sundberg84/AllHearingEar/hardware/3d model/Pyramid 0.2/20161116_210447.jpg

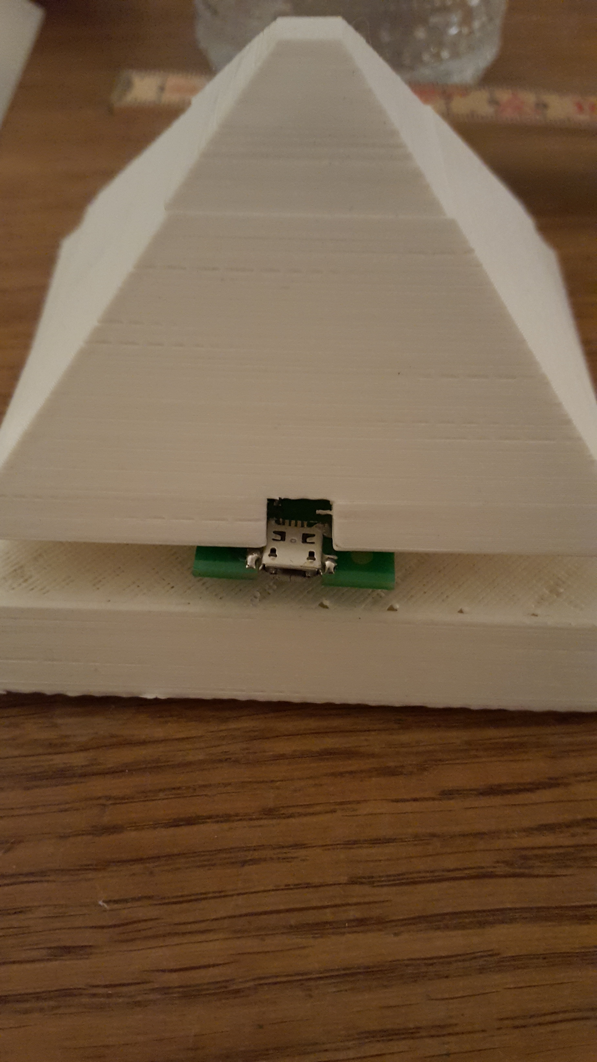
hardware/3d model/Pyramid 0.2/20161116_210447.jpg
