sundberg84/AllHearingEar/hardware/PCB/UsbSticka/Res/Max9814ada.JPG

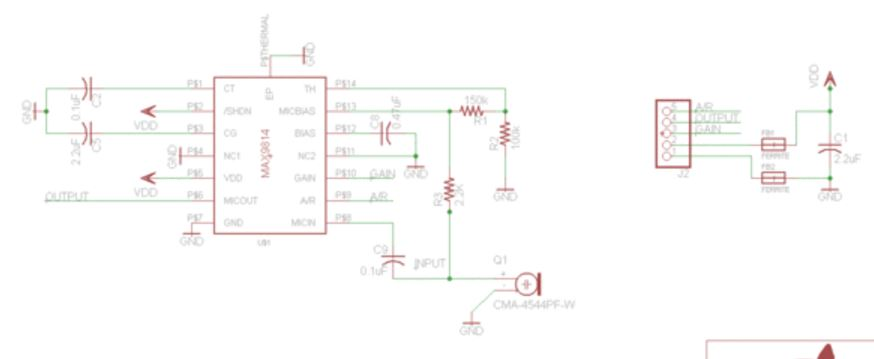
hardware/PCB/UsbSticka/Res/Max9814ada.JPG
