sundberg84/AllHearingEar/Pictures/3dPyraLong.JPG

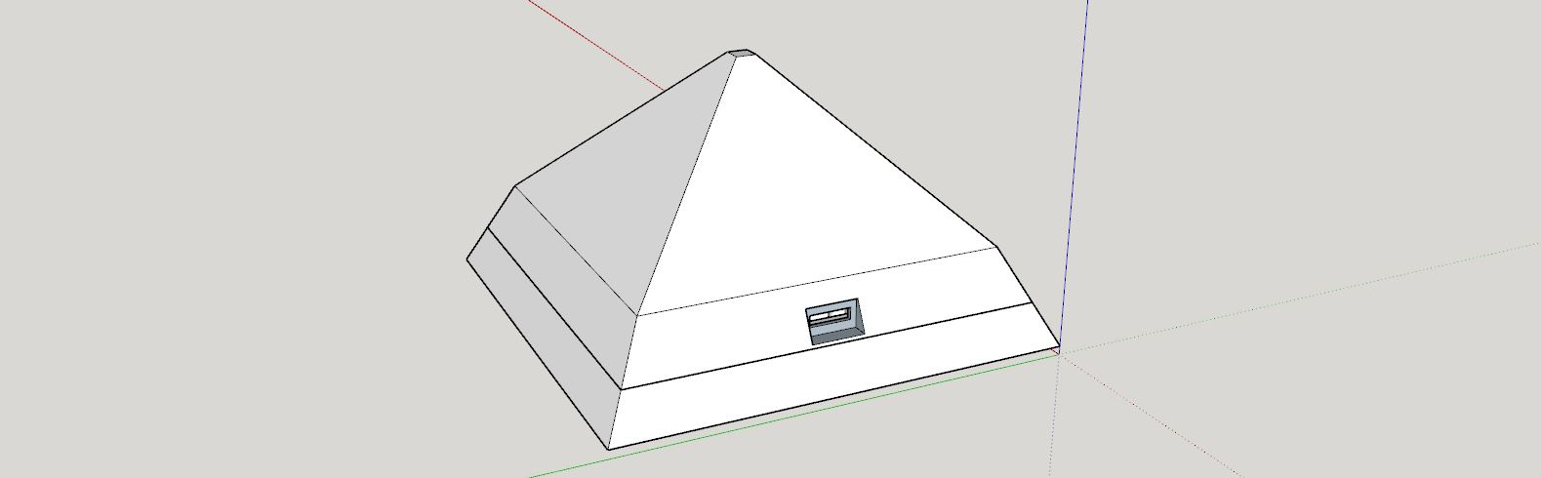
Pictures/3dPyraLong.JPG
