sundberg84/AllHearingEar/Pictures/3dPyraSquare.JPG

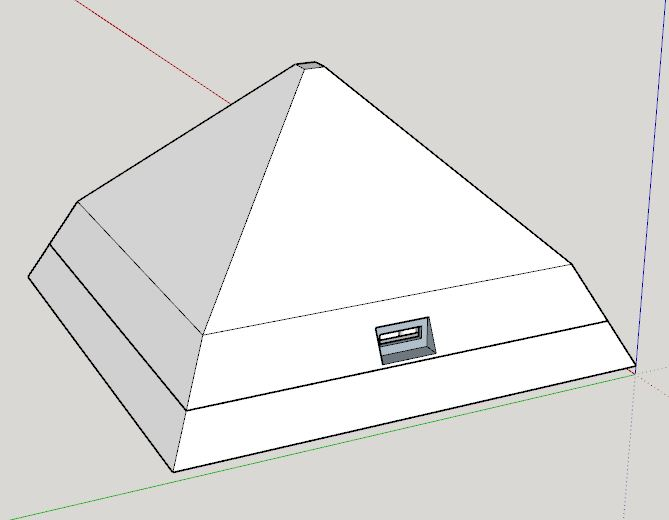
Pictures/3dPyraSquare.JPG
