sundberg84/AllHearingEar/Pictures/20160913_220625.jpg

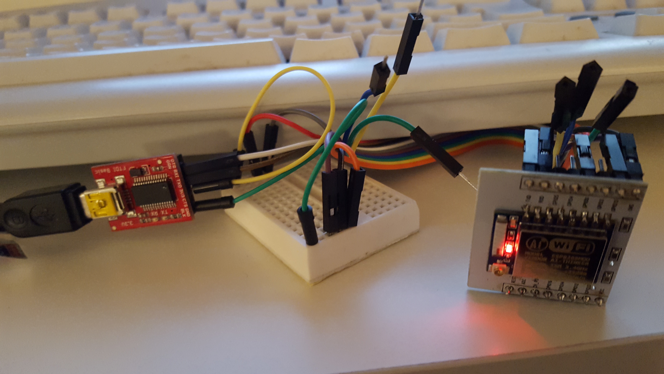
Pictures/20160913_220625.jpg
