sundberg84/AllHearingEar/Pictures/20160926_PCBtest.JPG

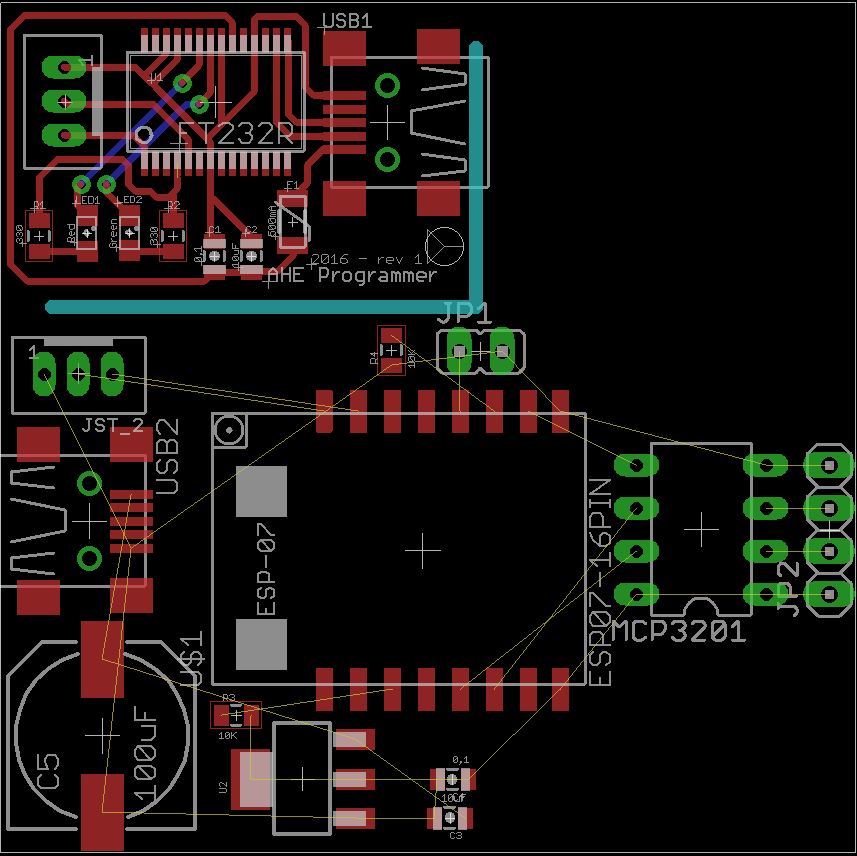
Pictures/20160926_PCBtest.JPG
