sundberg84/AllHearingEar/Pictures/20161007_163945.jpg

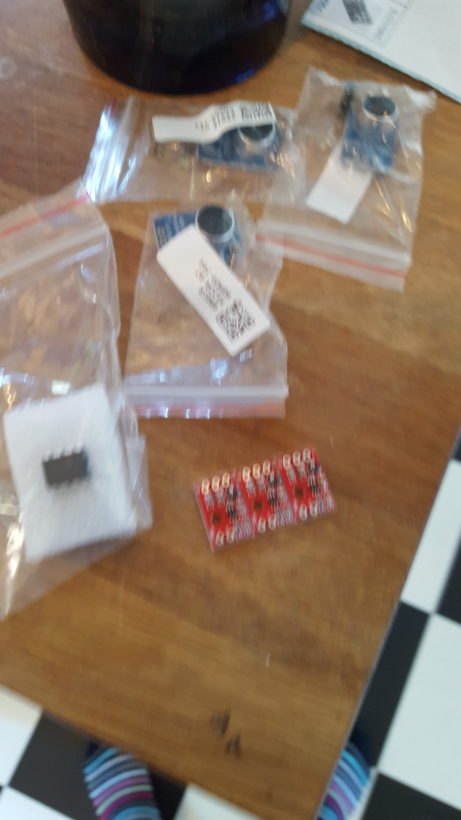
Pictures/20161007_163945.jpg
