sundberg84/AllHearingEar/Pictures/20161007_164515.jpg

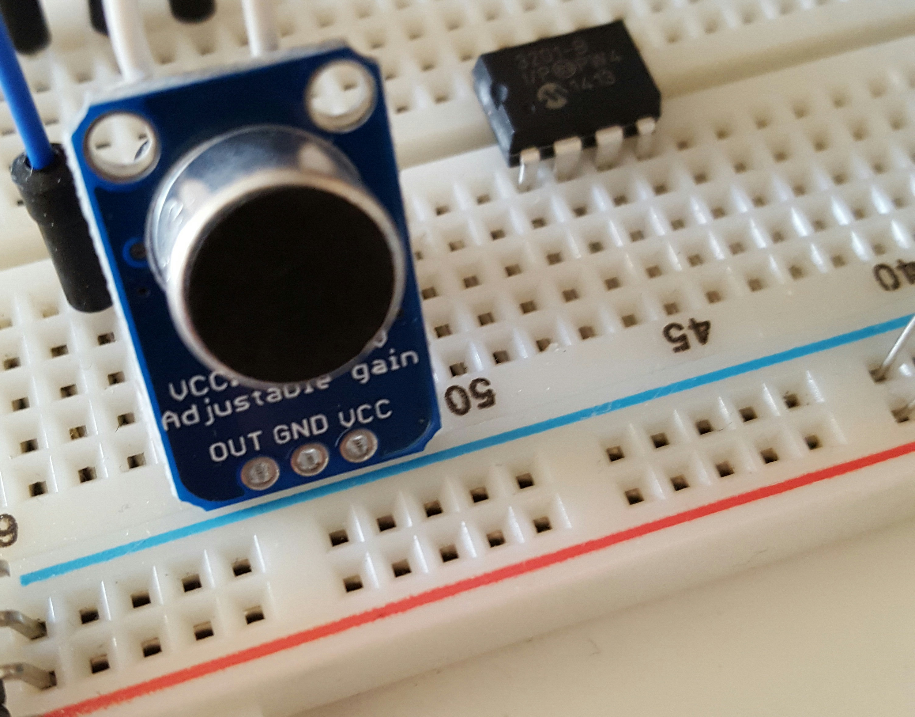
Pictures/20161007_164515.jpg
