sundberg84/AllHearingEar/Pictures/20161008_091315.jpg

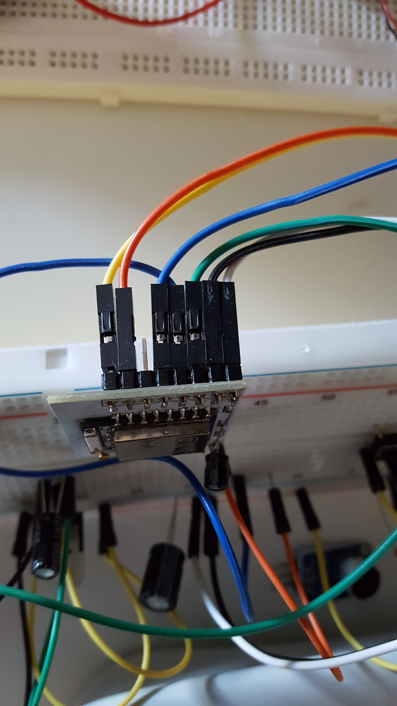
Pictures/20161008_091315.jpg
