sundberg84/AllHearingEar/Pictures/20161018_220418.jpg

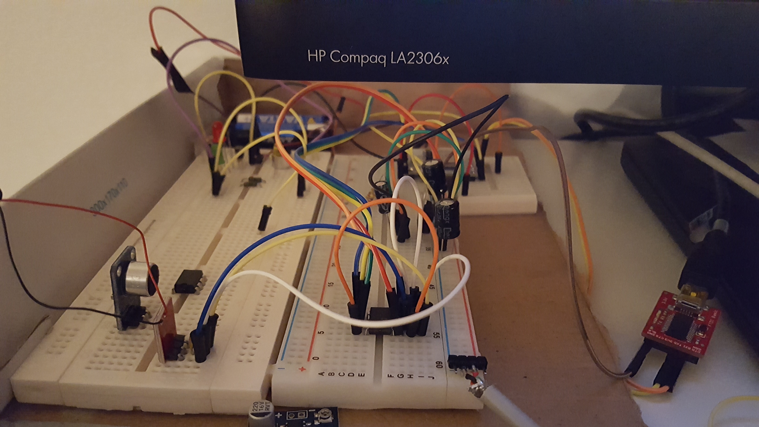
Pictures/20161018_220418.jpg
