sundberg84/AllHearingEar/Pictures/AllHearingEarPcSoftware.jpg

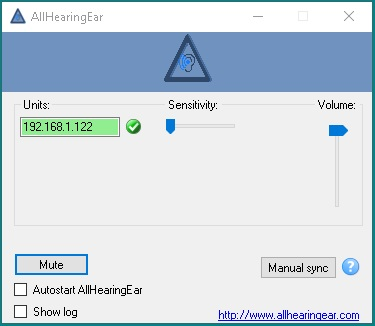
Pictures/AllHearingEarPcSoftware.jpg
