sundberg84/AllHearingEar/Pictures/comic.png

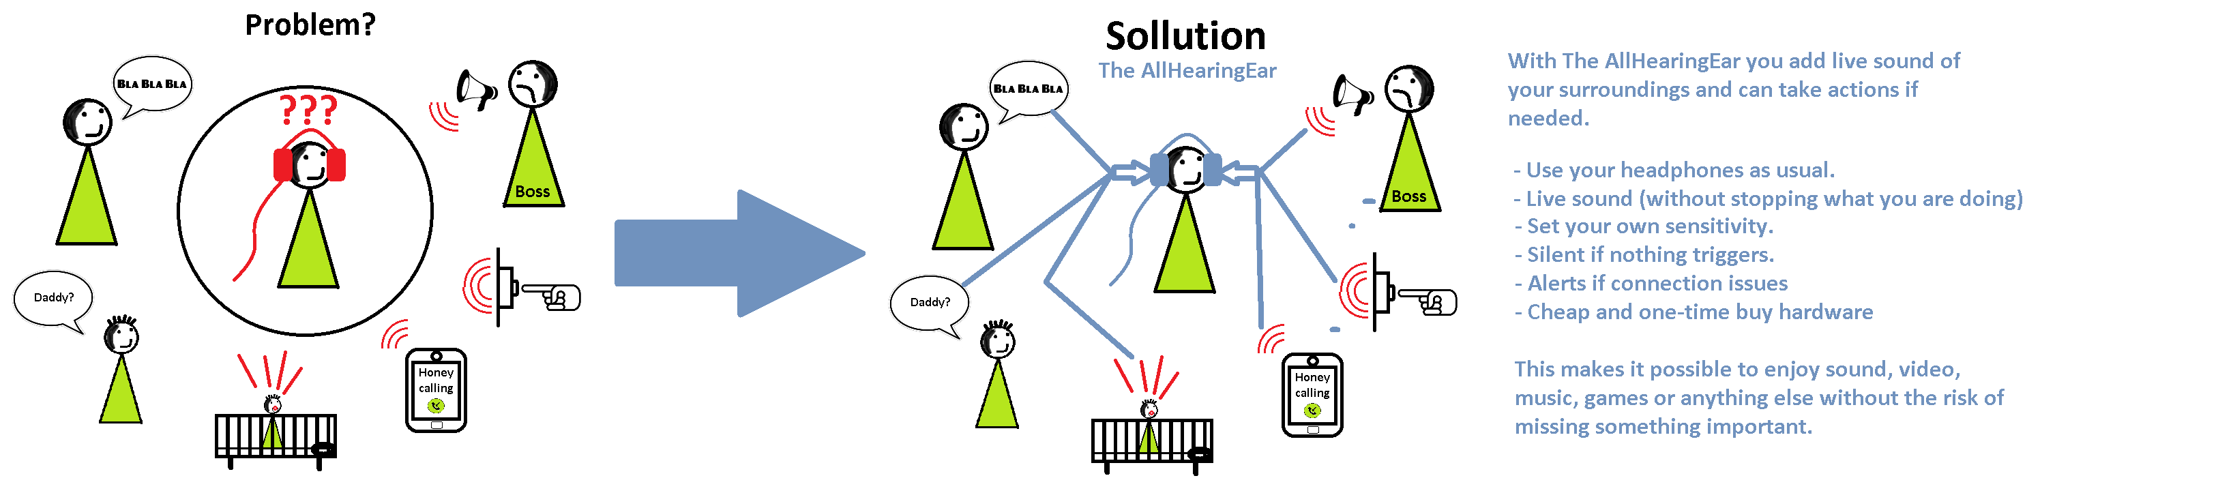
Pictures/comic.png
