sundberg84/AllHearingEar/Pictures/earplugs.jpg

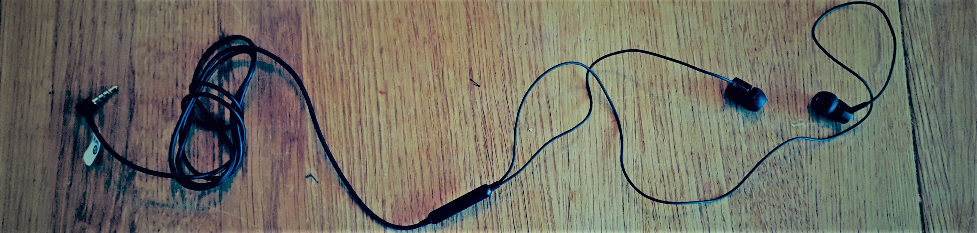
Pictures/earplugs.jpg
