sundberg84/AllHearingEar/Pictures/headphones1small.jpg

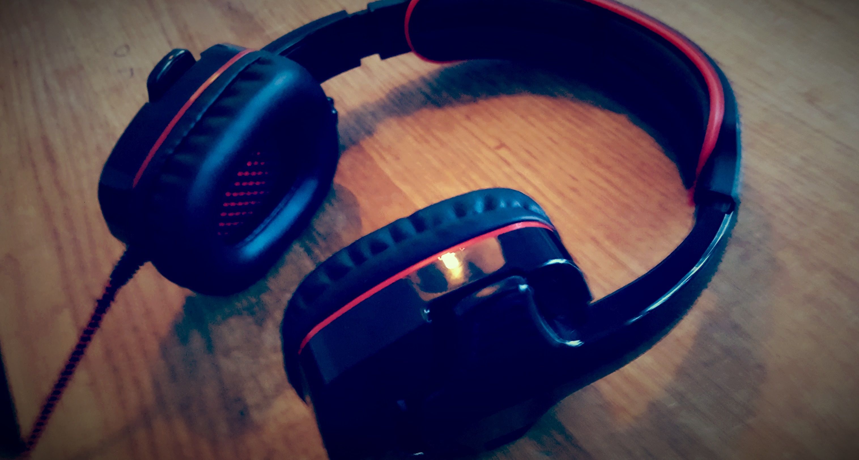
Pictures/headphones1small.jpg
