sundberg84/AllHearingEar/Pictures/headphones2.jpg

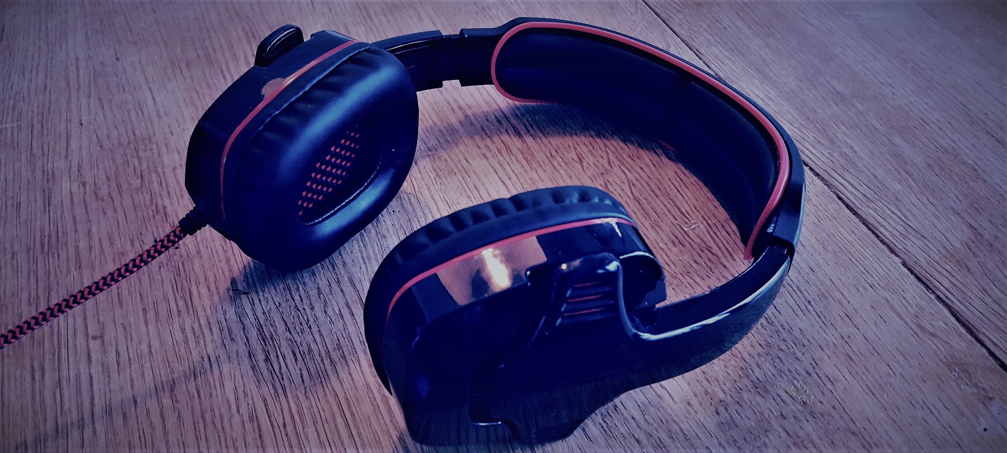
Pictures/headphones2.jpg
