sundberg84/AllHearingEar/Pictures/headphones2_neo.jpg

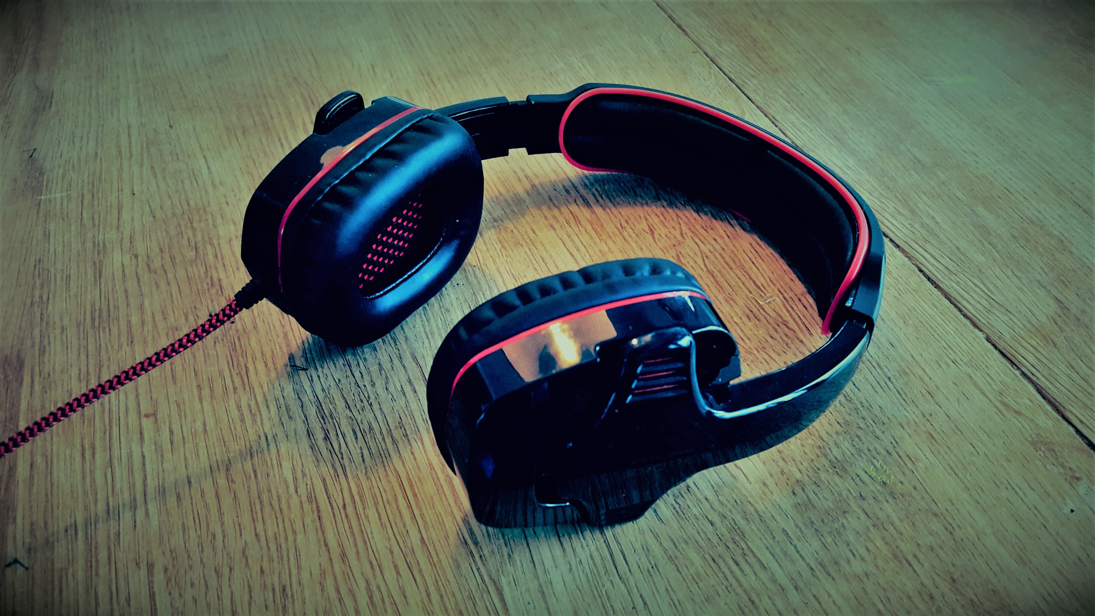
Pictures/headphones2_neo.jpg
