sundberg84/AllHearingEar/Pictures/Pyramid06_1.png

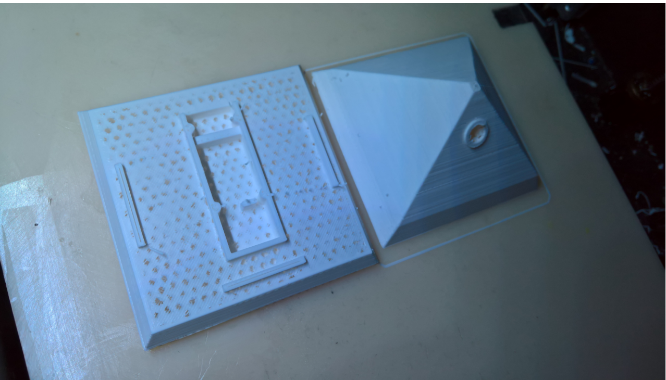
Pictures/Pyramid06_1.png
