sundberg84/AllHearingEar/Pictures/slider2.jpg

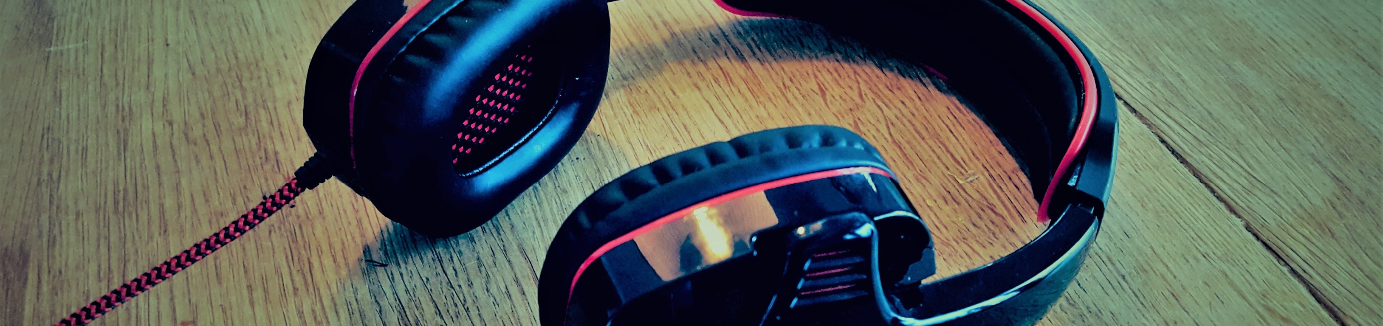
Pictures/slider2.jpg
