sundberg84/AllHearingEar/Pictures/slider3.jpg

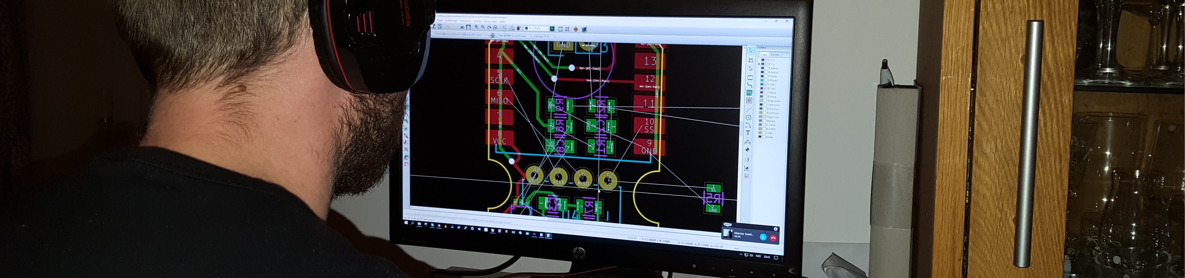
Pictures/slider3.jpg
