sundberg84/AllHearingEar/Pictures/slider4.jpg

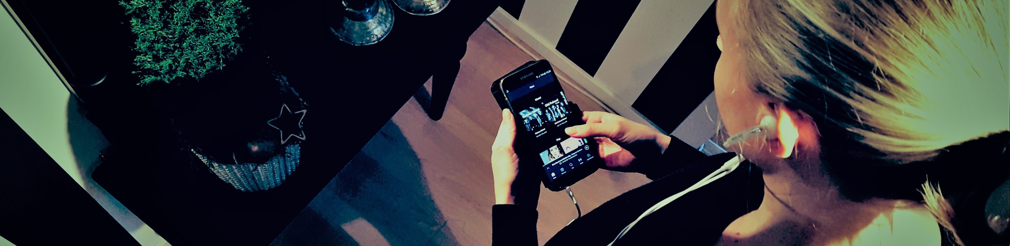
Pictures/slider4.jpg
