sundberg84/AllHearingEar/Pictures/Sticks.png

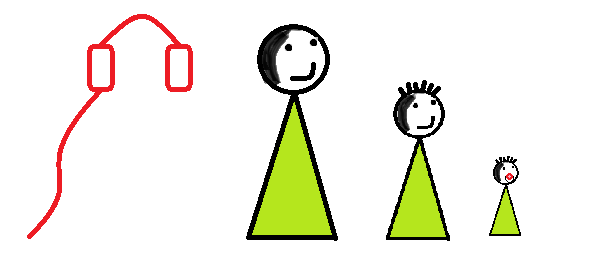
Pictures/Sticks.png
