sundberg84/AllHearingEar/software/Android/Files/pyr_connected.png

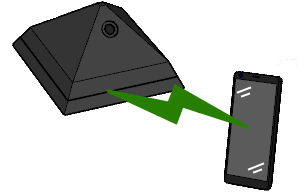
software/Android/Files/pyr_connected.png
