sundberg84/AllHearingEar/hardware/3d model/Pyramid 0.5/Pyramid 0.5.stl

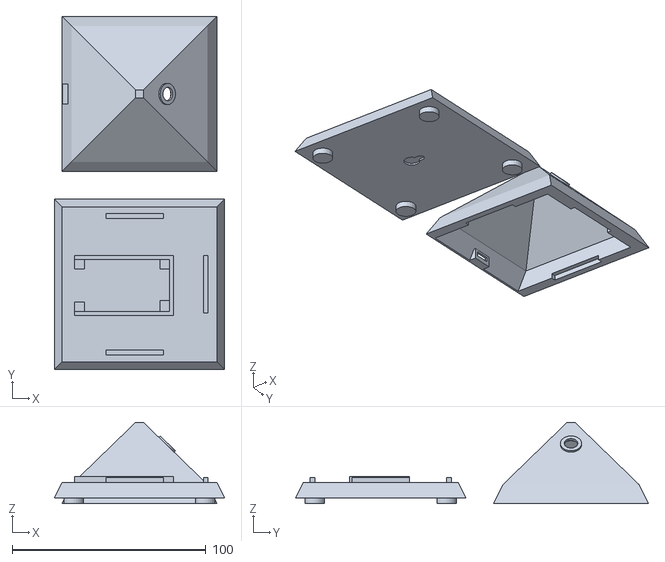
[picture p47: CAD file, 2017-01-01]
hardware/3d model/Pyramid 0.5/Pyramid 0.5.stl
88.0 x 182.2 x 42.0
