sundberg84/AllHearingEar/hardware/PCB/UsbSticka/01dev/01dev_long_microUSB.kicad_pcb

## KiCad design hardware/PCB/UsbSticka/01dev/01dev_long_microUSB.kicad_pcb (2017-01-03)

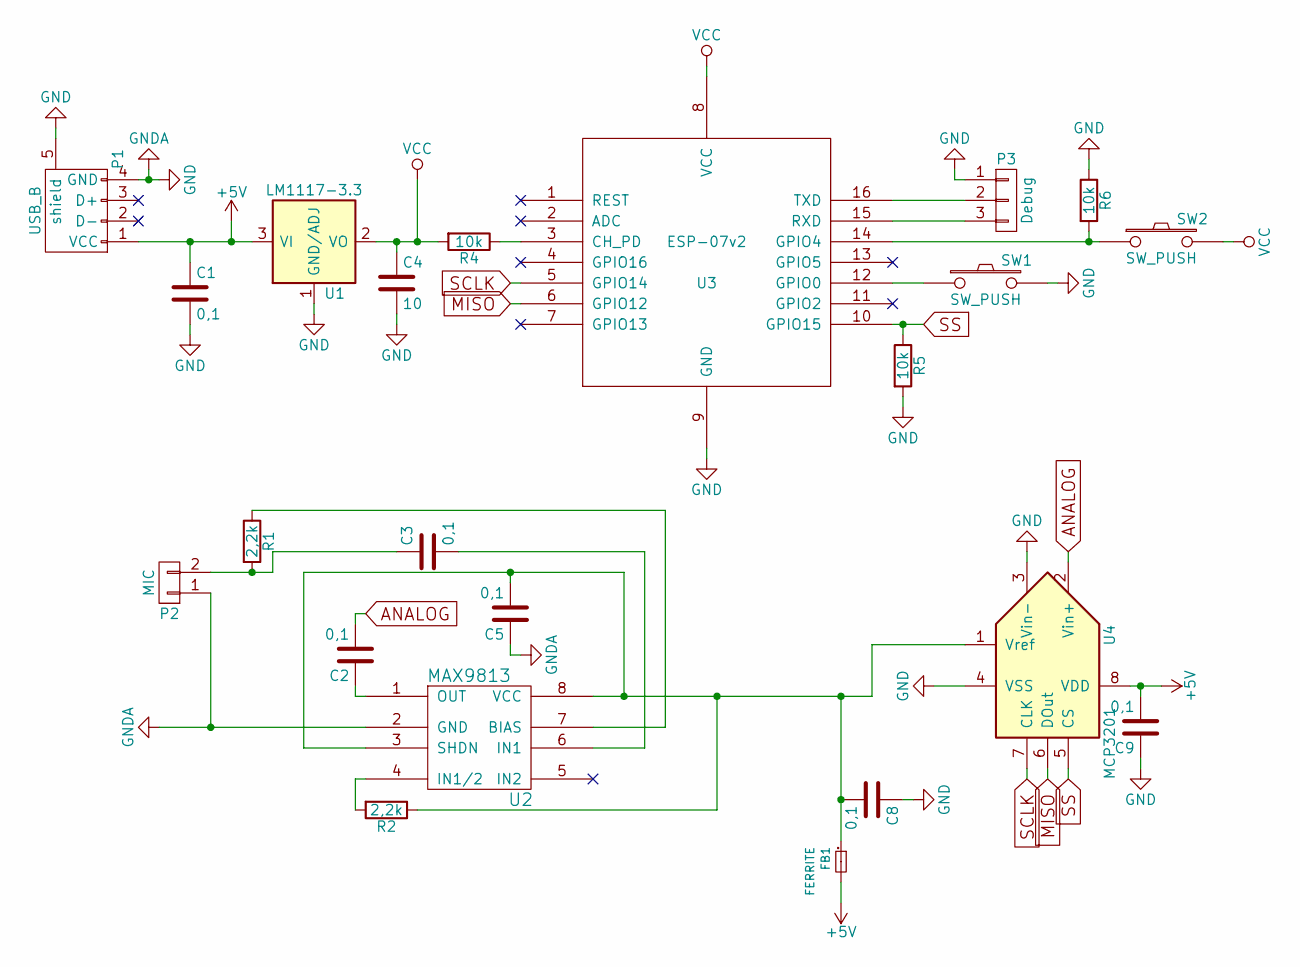
[picture p65: schematic 01dev.sch]

Parts:
C1, C2, C3, C5, C8, C9: 0,1; C_0805
C4: 10; C_0805
FB1: FERRITE; C_0805_HandSoldering
P1: USB_B; USB_Micro-B
P2: MIC; Socket_Strip_Straight_1x02
P3: Debug; Socket_Strip_Straight_1x03
R1, R2: 2,2k; R_0805
R4, R5, R6: 10k; R_0805
SW1, SW2: SW_PUSH; SW_SPST_EVQPE1
U1: LM1117-3.3; SOT-223
U2: MAX9813; SOT-23-8
U3: ESP-07v2; ESP-07_AS
U4: MCP3201; PDIP-8

Connections:
+5V: C1.1, C9.2, FB1.2, P1.1 (VCC), U1.3 (VI), U4.8 (VDD)
ANALOG: C2.2, U4.2 (Vin+)
GND: C1.2, C4.2, C5.1, C8.1, C9.1, P1.4 (GND), P1.5 (shield), P2.1, P3.1, R5.2, R6.1, SW1.2, U1.1 (GND/ADJ), U2.2 (GND), U3.9 (GND), U4.3 (Vin-), U4.4 (VSS); also elsewhere on the board
MISO: U3.6 (GPIO12), U4.6 (DOut)
unnamed: C2.1, U2.1 (OUT)
unnamed: C3.1, P2.2, R1.2
unnamed: C3.2, U2.6 (IN1)
unnamed: C5.2, C8.2, FB1.1, R2.1, U2.3 (SHDN), U2.8 (VCC), U4.1 (Vref)
unnamed 8: P3.2, U3.16 (TXD); also elsewhere on the board
unnamed 9: P3.3, U3.15 (RXD); also elsewhere on the board
unnamed: R1.1, U2.7 (BIAS)
unnamed: R2.2, U2.4 (IN1/2)
unnamed: R4.1, U3.3 (CH_PD)
unnamed: R6.2, SW2.1, U3.14 (GPIO4)
unnamed: SW1.1, U3.12 (GPIO0)
SCLK: U3.5 (GPIO14), U4.7 (CLK)
SS: R5.1, U3.10 (GPIO15), U4.5 (CS)
VCC: C4.1, R4.2, SW2.2, U1.2 (VO), U1.4 (VO), U3.8 (VCC)

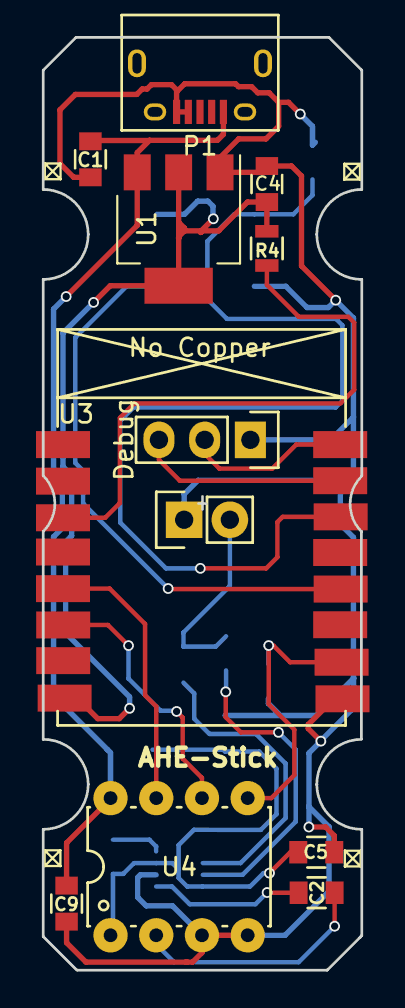
[picture p66: board 01dev_long_microUSB.kicad_pcb from above]

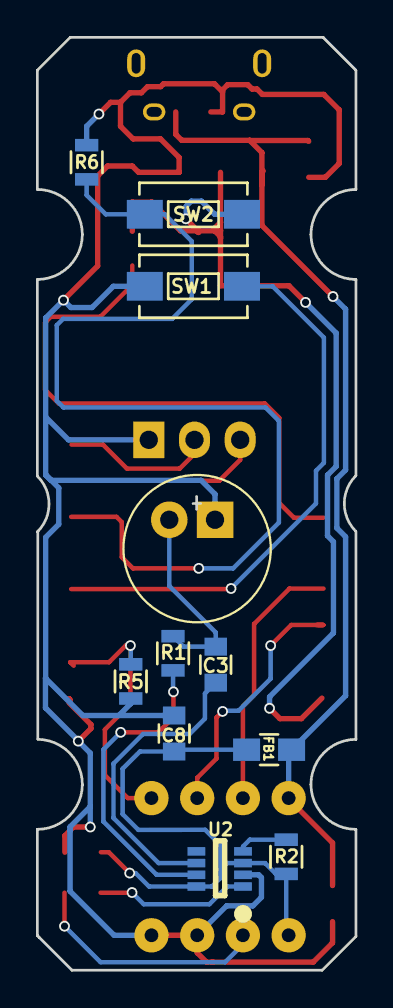
[picture p67: board 01dev_long_microUSB.kicad_pcb from below]

Board: 2 copper layers, 17.7 x 51.8 mm, 22 parts (10 on the bottom side), 18 nets.

Other parts of the board:
Debug: Debug; Socket_Strip_Straight_1x03

Their connections:
GND: Debug.1; also elsewhere on the board
unnamed 8: Debug.2; also elsewhere on the board
unnamed 9: Debug.3; also elsewhere on the board
