sundberg84/AllHearingEar/software/Android/Objects/shell/src/b4a/example/main.java

package b4a.example;

import java.io.IOException;
import anywheresoftware.b4a.BA;
import anywheresoftware.b4a.pc.PCBA;
import anywheresoftware.b4a.pc.RDebug;
import anywheresoftware.b4a.pc.RemoteObject;
import anywheresoftware.b4a.pc.RDebug.IRemote;
import anywheresoftware.b4a.pc.Debug;

public class main implements IRemote{
	public static main mostCurrent;
	public static RemoteObject processBA;
    public static boolean processGlobalsRun;
    public static RemoteObject myClass;
    public static RemoteObject remoteMe;
	public main() {
		mostCurrent = this;
	}
    public RemoteObject getRemoteMe() {
        return remoteMe;    
    }
    
	public static void main (String[] args) throws Exception {
		new RDebug(args[0], Integer.parseInt(args[1]), Integer.parseInt(args[2]), args[3]);
		RDebug.INSTANCE.waitForTask();

	}
    static {
        anywheresoftware.b4a.pc.RapidSub.moduleToObject.put("b4a.example.main", "b4a.example.main");
	}

public boolean isSingleton() {
		return true;
	}
     public static RemoteObject getObject() {
		return myClass;
	 }

	public RemoteObject activityBA;
	public RemoteObject _activity;
    private PCBA pcBA;

	public PCBA create(Object[] args) throws ClassNotFoundException{
		processBA = (RemoteObject) args[1];
		activityBA = (RemoteObject) args[2];
		_activity = (RemoteObject) args[3];
        anywheresoftware.b4a.keywords.Common.Density = (Float)args[4];
        remoteMe = (RemoteObject) args[5];
		pcBA = new PCBA(this, main.class);
        main_subs_0.initializeProcessGlobals();
		return pcBA;
	}
public static RemoteObject __c = RemoteObject.declareNull("anywheresoftware.b4a.keywords.Common");
public static RemoteObject _imageview1 = RemoteObject.declareNull("anywheresoftware.b4a.objects.ImageViewWrapper");
public static RemoteObject _btnmanual = RemoteObject.declareNull("anywheresoftware.b4a.objects.ButtonWrapper");
public static RemoteObject _btnsync = RemoteObject.declareNull("anywheresoftware.b4a.objects.ButtonWrapper");
public static RemoteObject _btnmute = RemoteObject.declareNull("anywheresoftware.b4a.objects.ButtonWrapper");
public static RemoteObject _edittext1 = RemoteObject.declareNull("anywheresoftware.b4a.objects.EditTextWrapper");
public static RemoteObject _lblunit1 = RemoteObject.declareNull("anywheresoftware.b4a.objects.LabelWrapper");
public static RemoteObject _lblunit2 = RemoteObject.declareNull("anywheresoftware.b4a.objects.LabelWrapper");
public static RemoteObject _lblunit3 = RemoteObject.declareNull("anywheresoftware.b4a.objects.LabelWrapper");
public static RemoteObject _lblunit4 = RemoteObject.declareNull("anywheresoftware.b4a.objects.LabelWrapper");
public static RemoteObject _pnlunits = RemoteObject.declareNull("anywheresoftware.b4a.objects.PanelWrapper");
public static RemoteObject _panel1 = RemoteObject.declareNull("anywheresoftware.b4a.objects.PanelWrapper");
public static RemoteObject _imgconstat = RemoteObject.declareNull("anywheresoftware.b4a.objects.ImageViewWrapper");
public static RemoteObject _sbsens = RemoteObject.declareNull("anywheresoftware.b4a.objects.SeekBarWrapper");
public static RemoteObject _mute = RemoteObject.createImmutable(false);
public static RemoteObject _green = RemoteObject.createImmutable(0);
public static RemoteObject _red = RemoteObject.createImmutable(0);
public static RemoteObject _manualip = RemoteObject.createImmutable("");
public static RemoteObject _ime = RemoteObject.declareNull("anywheresoftware.b4a.objects.IME");
public static RemoteObject _txtmanip = RemoteObject.declareNull("anywheresoftware.b4a.objects.EditTextWrapper");
public static RemoteObject _btnok = RemoteObject.declareNull("anywheresoftware.b4a.objects.ButtonWrapper");
public static RemoteObject _sens = RemoteObject.createImmutable("");
public static b4a.example.udpmodul _udpmodul = null;
  public Object[] GetGlobals() {
		return new Object[] {"Activity",main.mostCurrent._activity,"btnManual",main.mostCurrent._btnmanual,"btnMute",main.mostCurrent._btnmute,"btnOK",main.mostCurrent._btnok,"btnSync",main.mostCurrent._btnsync,"EditText1",main.mostCurrent._edittext1,"green",main._green,"ImageView1",main.mostCurrent._imageview1,"IME",main.mostCurrent._ime,"imgConStat",main.mostCurrent._imgconstat,"lblUnit1",main.mostCurrent._lblunit1,"lblUnit2",main.mostCurrent._lblunit2,"lblUnit3",main.mostCurrent._lblunit3,"lblUnit4",main.mostCurrent._lblunit4,"ManualIP",main.mostCurrent._manualip,"mute",main._mute,"Panel1",main.mostCurrent._panel1,"pnlUnits",main.mostCurrent._pnlunits,"red",main._red,"SBSens",main.mostCurrent._sbsens,"Sens",main.mostCurrent._sens,"txtManIP",main.mostCurrent._txtmanip,"UDPmodul",Debug.moduleToString(b4a.example.udpmodul.class)};
}
}
